gxurma/HighPrecPosSens/Test/measurement data/5-14.csv

Time | x
s | logic
-0.0004999992 | 53.
-0.0004998392 | 53.
-0.0004996792 | 53.
-0.0004995192 | 53.
-0.0004993592 | 53.
-0.0004991992 | 53.
-0.0004990392 | 53.
-0.0004988792 | 53.
-0.0004987192 | 53.
-0.0004985592 | 53.
-0.0004983992 | 131.
-0.0004982392 | 138.
-0.0004980792 | 144.
-0.0004979192 | 144.
-0.0004977592 | 149.
-0.0004975992 | 152.
-0.0004974392 | 154.
-0.0004972792 | 156.
-0.0004971192 | 156.
-0.0004969592 | 156.
-0.0004967992 | 157.
-0.0004966392 | 157.
-0.0004964792 | 157.
-0.0004963192 | 157.
-0.0004961592 | 158.
-0.0004959992 | 157.
-0.0004958392 | 158.
-0.0004956792 | 158.
-0.0004955192 | 158.
-0.0004953592 | 158.
-0.0004951992 | 158.
-0.0004950392 | 158.
-0.0004948792 | 158.
-0.0004947192 | 158.
-0.0004945592 | 159.
-0.0004943992 | 159.
-0.0004942392 | 158.
-0.0004940792 | 159.
-0.0004939192 | 159.
-0.0004937592 | 158.
-0.0004935992 | 158.
-0.0004934392 | 158.
-0.0004932792 | 158.
-0.0004931192 | 158.
-0.0004929592 | 159.
-0.0004927992 | 158.
-0.0004926392 | 159.
-0.0004924792 | 158.
-0.0004923192 | 158.
-0.0004921592 | 158.
-0.0004919992 | 158.
-0.0004918392 | 159.
-0.0004916792 | 157.
-0.0004915192 | 157.
-0.0004913592 | 159.
-0.0004911992 | 158.
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
