gxurma/HighPrecPosSens/PCB/HighPrecPosSensDev/Gerber/HighPrecPosSens-F_Fab.pdf

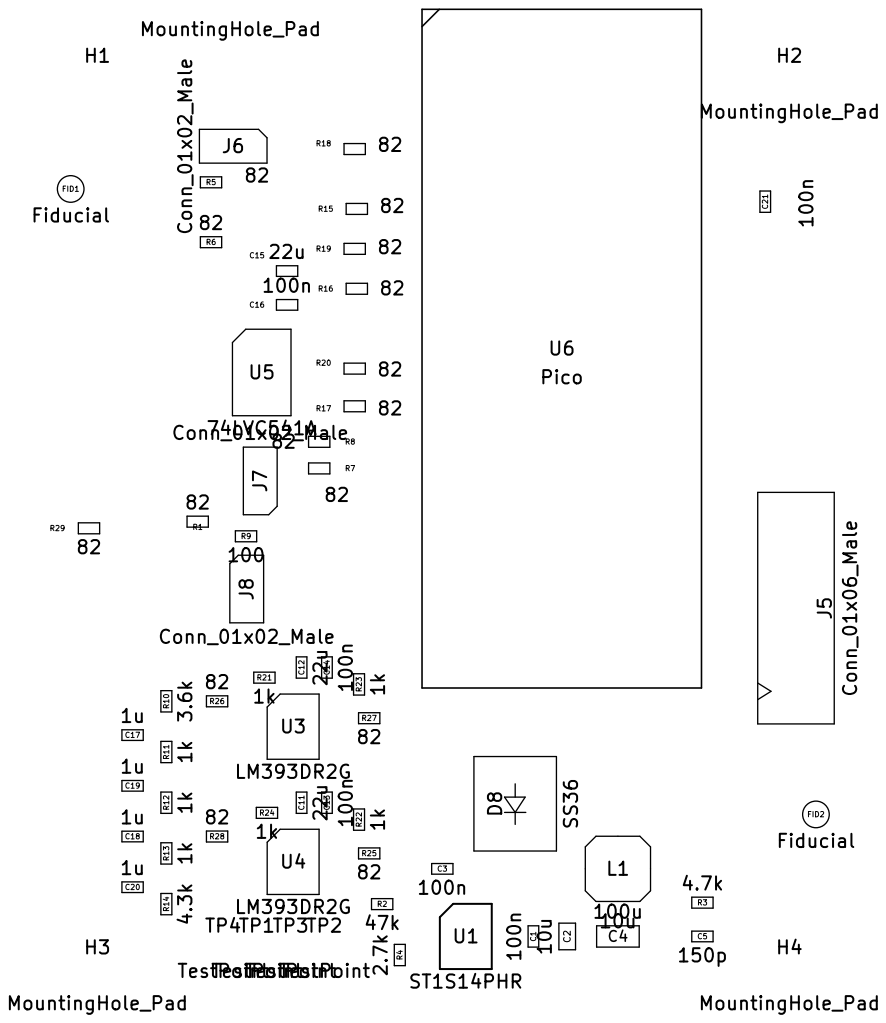
[picture p11: page 1]

File: HighPrecPosSens.kicad_pcb Sheet: enGyneer

Id: 1/1 Title: High Precision Position Sensor
