gxurma/HighPrecPosSens/PCB/HighPrecPosSensDev/Gerber/HighPrecPosSens-F_Paste.pdf

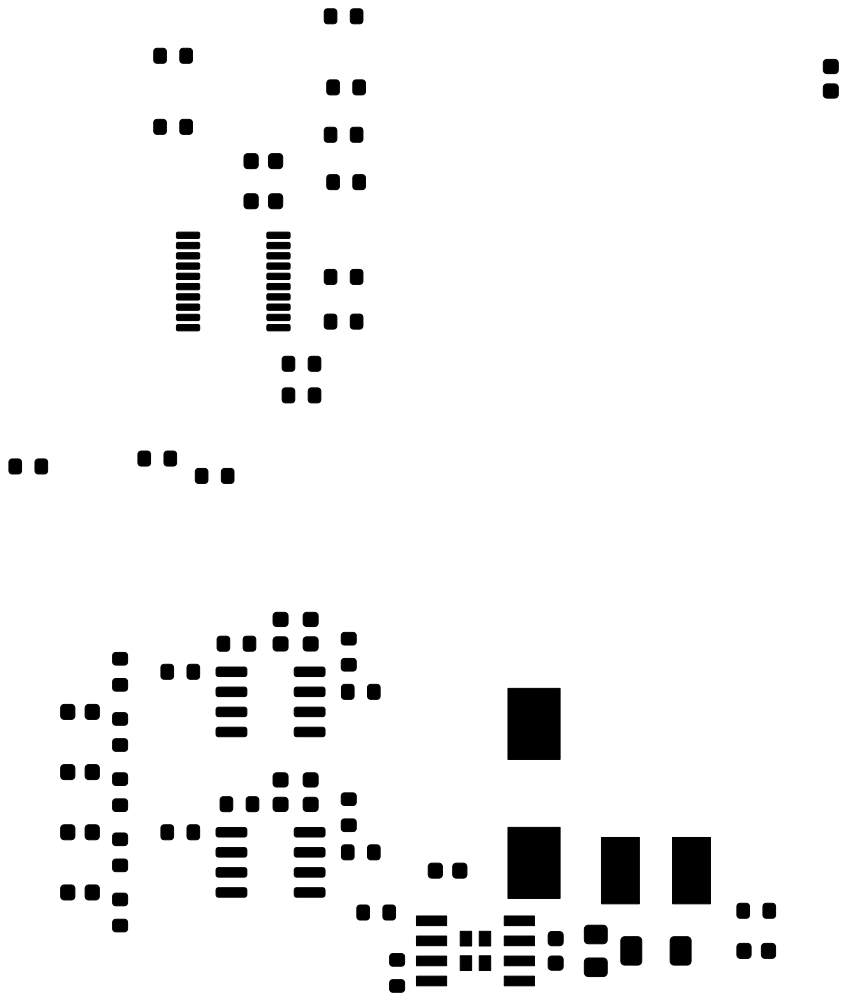
[picture p13: page 1]

File: HighPrecPosSens.kicad_pcb Sheet: enGyneer

Id: 1/1 Title: High Precision Position Sensor
