gxurma/HighPrecPosSens/PCB/HighPrecPosSensDev/Gerber/HighPrecPosSens-F_Silkscreen.pdf

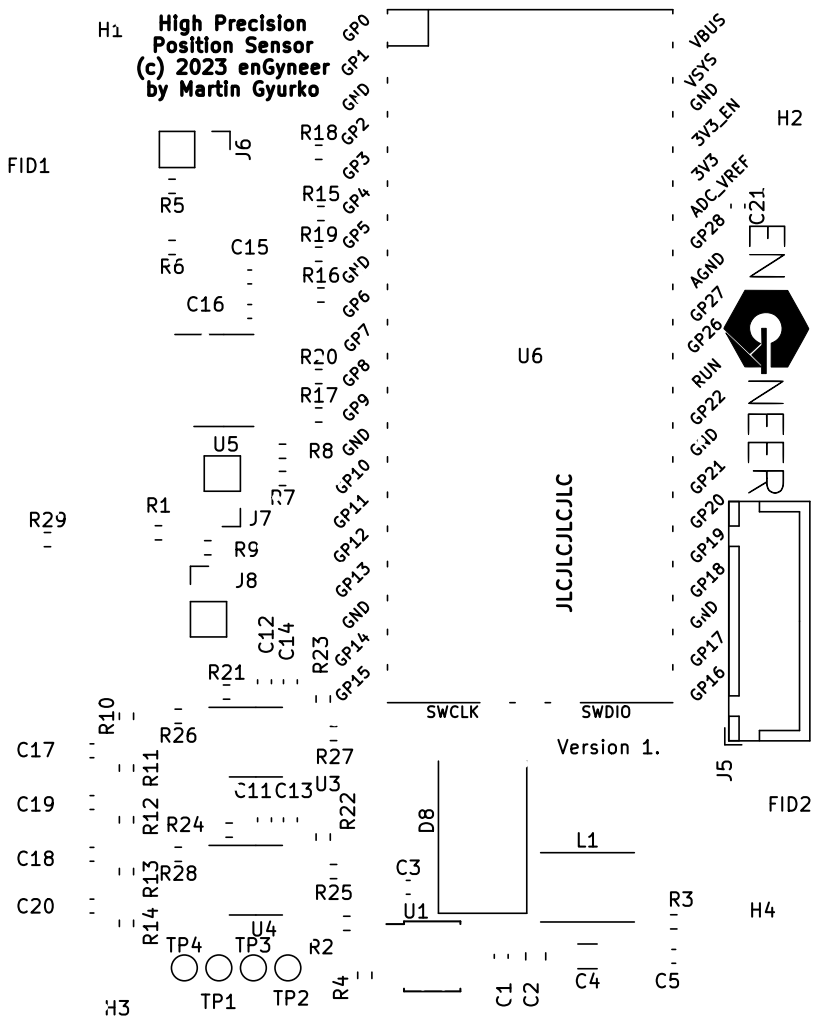
[picture p14: page 1]

High Precision Position Sensor

File: HighPrecPosSens.kicad_pcb Sheet: enGyneer

Id: 1/1 Title: High Precision Position Sensor
