gxurma/HighPrecPosSens/Simulation/LM393Test.asc

R1: res; 1k
R2: res; 1k
R3: res; 5k
U1: opamp2; LM393
V1: voltage; 5
V2: voltage; SINE(0 {SIG} 1000 1u 1u 498u 1000)
Named nets: 0, +V, OUT, SIG, REF
.tran 10m startup
.inc LM393.5_1
.param SIG=5
