gxurma/HighPrecPosSens/Simulation/Comparator 2 bit ADC.asc

C1: cap; 1µ
C2: cap; 1µ
C3: cap; 1µ
C4: cap; 1µ
R1: res; 3.6k
R2: res; 1k
R3: res; 1k
R4: res; 1k
R5: res; 4.3k
R6: res; 5k
R7: res; 5k
R8: res; 5k
R9: res; 5k
R10: res; 100
R11: res; 1000
U1: UniversalOpAmp2; LM393; ""
U2: UniversalOpAmp2; LM393; ""
U3: UniversalOpAmp2; LM393; ""
U4: UniversalOpAmp2; LM393; ""
U5: LT1818
V1: voltage; 3.3
V2: voltage; SINE(1.75 0.53 250000 0 0 0 1000); AC 1 1
Named nets: 0
.tran 100u
.inc LM393.5_1
