gxurma/HighPrecPosSens/Firmware/dma_capture/code/calibrationfile.py

amin =  [55, 55, 55, 55, 55, 55, 55, 55, 55, 55, 55, 55, 56, 56, 56, 56, 56, 55, 56, 55, 56, 56, 56, 56, 56, 56, 56, 56, 56, 56, 56, 56, 56, 56, 56, 56, 56, 56, 56, 56, 56, 56, 56, 56, 56, 56, 56, 56, 56, 56, 56, 56, 56, 56, 56, 56, 56, 56, 56, 56, 56, 56, 56, 57, 56, 56, 57, 56, 56, 56, 57, 56, 57, 57, 57, 57, 57, 57, 57, 57, 57, 57, 57, 56, 57, 57, 57, 56, 57, 56, 57, 56, 56, 57, 57, 57, 57, 57, 57, 57, 57, 57, 56, 57, 57, 57, 57, 56, 57, 57, 57, 56, 57, 56, 57, 56, 57, 56, 57, 57, 57, 57, 57, 57, 57, 57, 57, 57, 57, 57, 57, 56, 57, 57, 57, 56, 57, 56, 57, 56, 56, 56, 57, 56, 57, 56, 56, 56, 57, 57, 56, 57, 57, 57, 57, 57, 57, 57, 57, 57, 57, 57, 57, 57, 57, 57, 57, 57, 57, 57, 57, 57, 57, 57, 57, 57, 57, 57, 57, 57, 57, 57, 57, 57, 57, 57, 57, 57, 57, 57, 57, 57, 57, 57, 57, 57, 57, 57, 57, 57, 57, 57, 57, 57, 57, 57, 57, 57, 57, 57, 57, 57, 57, 57, 57, 57, 57, 57, 57, 57, 57, 57, 57, 58, 57, 57, 57, 58, 57, 57, 58, 57, 58, 58, 57, 57, 57, 58, 57, 58, 58, 58, 58, 57, 58, 58, 58, 58, 58, 58, 58, 58, 58, 58, 58, 57, 58, 58, 57, 58, 58, 58, 58, 58, 58, 58, 57, 58, 58, 58, 58, 58, 58, 59, 58, 58, 59, 59, 59, 59, 59, 58, 59, 58, 59, 58, 58, 59, 58, 58, 58, 58, 58, 58, 58, 58, 58, 58, 58, 57, 58, 57, 57, 58, 58, 57, 57, 57, 58, 57, 57, 58, 58, 58, 58, 58, 58, 58, 58, 58, 58, 58, 59, 58, 58, 58, 59, 58, 59, 58, 58, 59, 58, 59, 59, 58, 59, 58, 58, 59, 59, 58, 59, 59, 59, 59, 59, 59, 58, 59, 58, 58, 59, 59, 59, 59, 59, 59, 59, 59, 59, 59, 59, 59, 59, 59, 60, 60, 59, 60, 60, 60, 59,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
 0, 0, 0, 0, 0, 0, 0, 0, 0, 0, 0, 0, 0, 0, 0, 0, 0, 0, 0, 0, 0, 0, 0, 0, 0, 0, 0, 0, 0, 0, 0, 0, 0, 0, 0, 0, 0, 0, 0, 0, 0, 0, 0, 0, 0, 0, 0, 0, 0, 0, 0, 0, 0, 0, 0, 0, 0, 0, 0, 0, 0, 0, 0, 0, 0, 0, 0, 0, 0, 0, 0, 0, 0, 0, 0, 0, 0, 0, 0, 0, 0, 0, 0, 0, 0, 0, 0, 0, 0, 0, 0, 0, 0, 0, 0, 0, 0, 0, 0, 0, 0, 0, 0, 0, 0, 0, 0, 0, 0, 0, 0, 0, 0, 0, 0, 0, 0, 0, 0, 0, 0, 0, 0, 0, 0, 0, 0, 0, 0, 0, 0, 0, 0, 0, 0, 0, 0, 0, 0, 0, 0, 0, 0, 0, 0, 0, 0, 0, 0, 0, 0, 0, 0, 0, 0, 0, 0, 0, 0, 0, 0, 0, 0, 0, 0, 0, 0, 0, 0, 0, 0, 0, 0, 0, 0, 0, 0, 0, 0, 0, 0, 0, 0, 0, 0, 0, 0, 0, 0, 0, 0, 0, 0, 0, 0, 0, 0, 0, 0, 0, 0, 0, 0, 0, 0, 0, 0, 0, 0, 0, 0, 0, 0, 0, 0, 0, 0, 0, 0, 0, 0, 0, 0, 0, 0, 0, 0, 0, 0, 0]
